sparkfun/SparkFun_GNSS_mosaic-G5_P3/Hardware/Dimensions.png

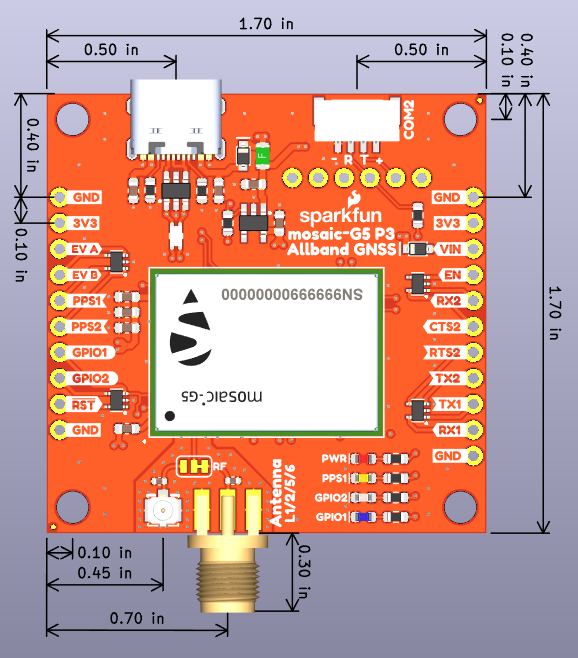
Hardware/Dimensions.png
